goscickiw/Analog-Video-Comb-Filter/pictures/photos/IMG_20240814_213257.JPG

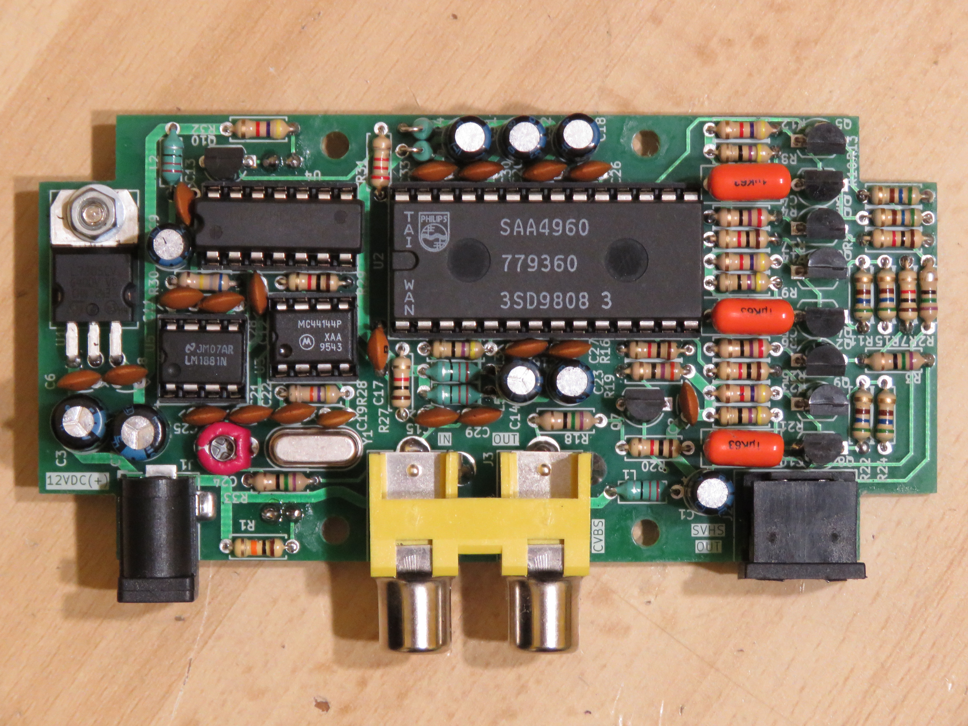
pictures/photos/IMG_20240814_213257.JPG
