goscickiw/Analog-Video-Comb-Filter/pictures/photos/IMG_20240814_214312.JPG

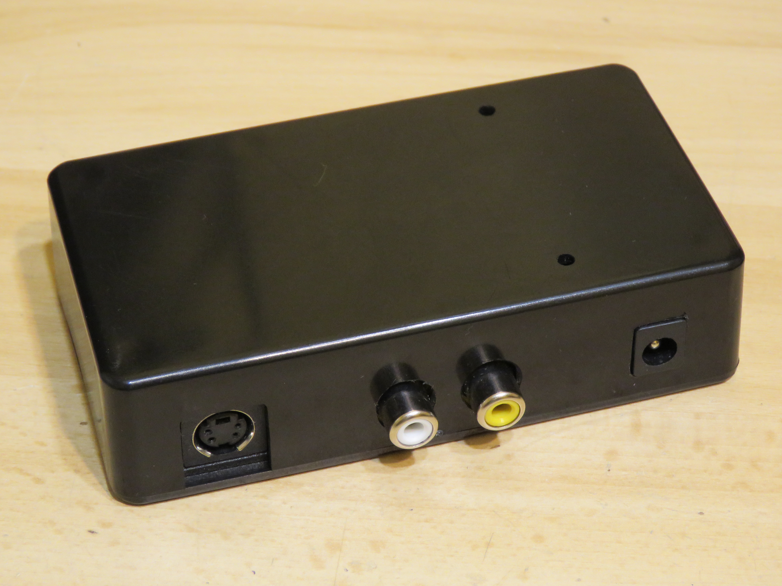
pictures/photos/IMG_20240814_214312.JPG
